yxysjtu/data-collection-device/code/include.h

#ifndef INCLUDE_H
#define INCLUDE_H

#include "main.h"
#include "adc.h"
#include "fatfs.h"
#include "i2c.h"
#include "rtc.h"
//#include "spi.h"
#include "usart.h"
#include "usb_device.h"
#include "gpio.h"

#include "stdio.h"
int fputc(int ch, FILE *f);

#include "sht30.h"
#include "bh1750.h"
#include "myadc.h"
#include "Flash.h"
#include "myrtc.h"
#include "w25q128.h"
#include "oled.h"
//#include "myspi.h"
//#include "sd.h"
//#include "sdff.h"


#endif
